JoshSilver8/MPPT-Charge-Controller/Photos/3D Model Rev 2.png

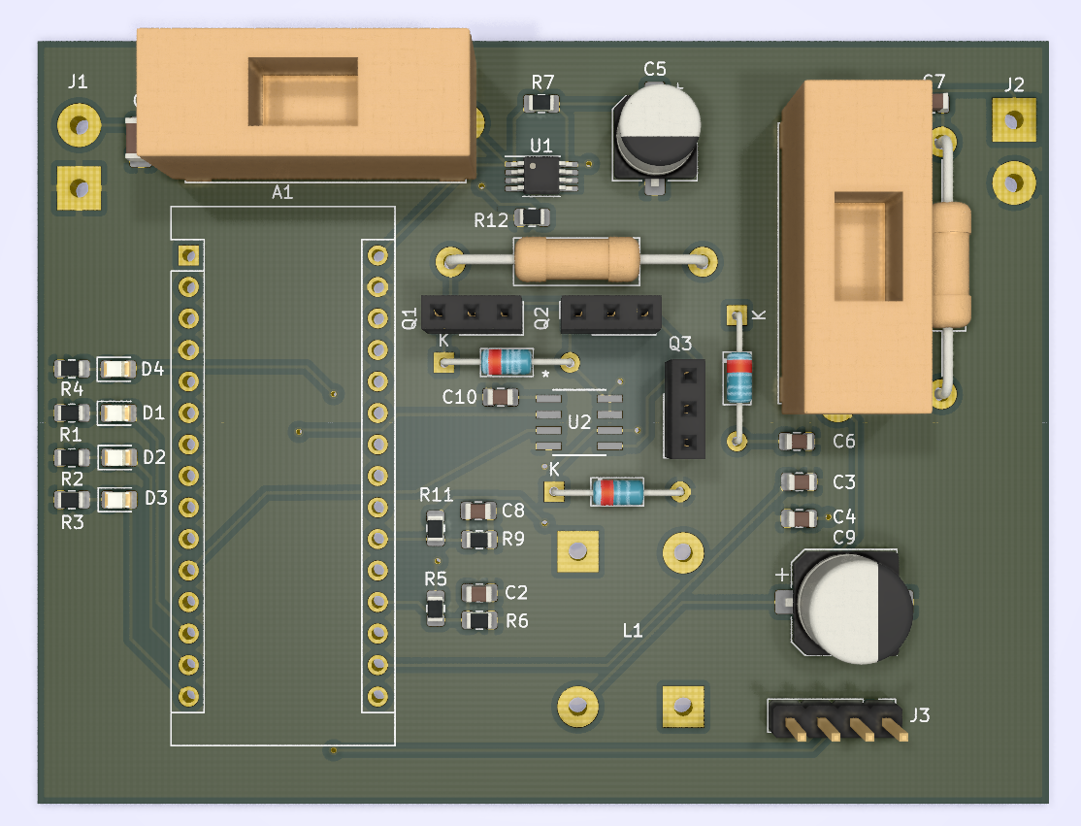
Photos/3D Model Rev 2.png
