JoshSilver8/MPPT-Charge-Controller/Photos/Buck Converter.png

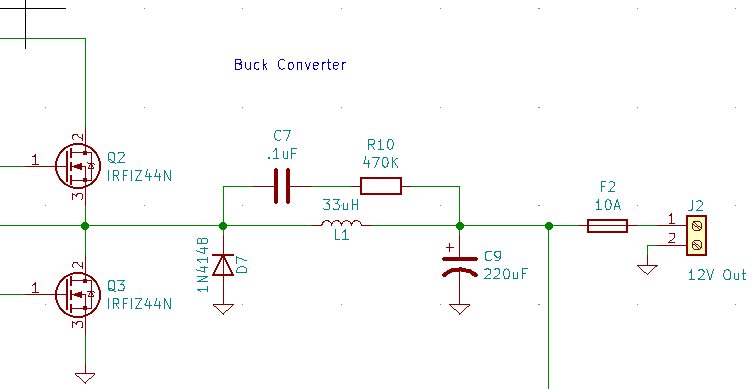
Photos/Buck Converter.png
