JoshSilver8/MPPT-Charge-Controller/Photos/Current and Voltage Sense.png

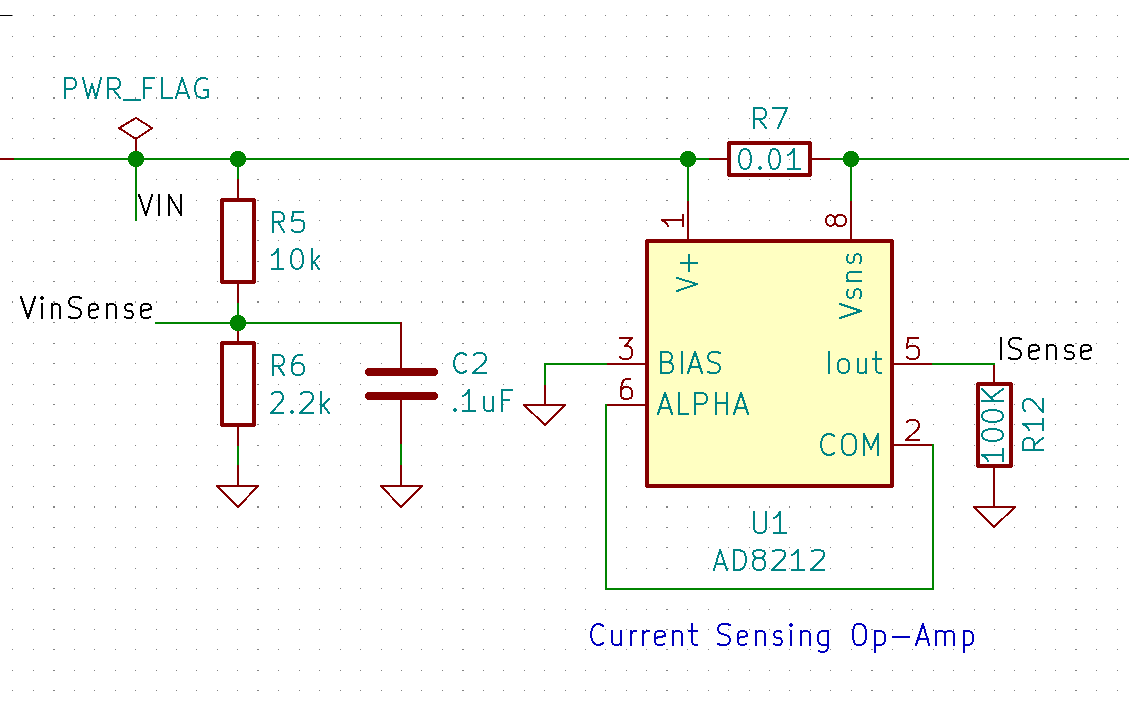
Photos/Current and Voltage Sense.png
