JoshSilver8/MPPT-Charge-Controller/Photos/Current Sense Config.png

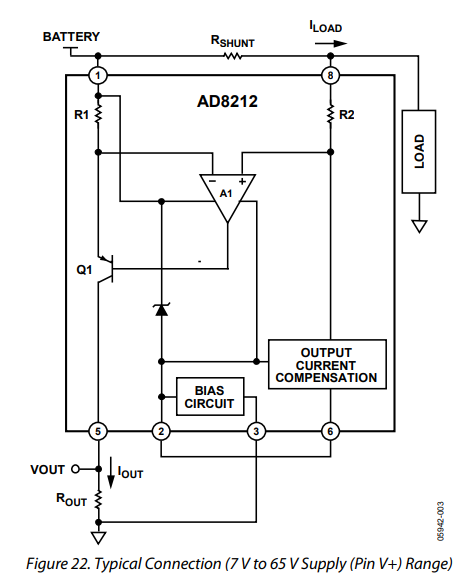
Photos/Current Sense Config.png
