JoshSilver8/MPPT-Charge-Controller/Photos/Discharge Prevention.png

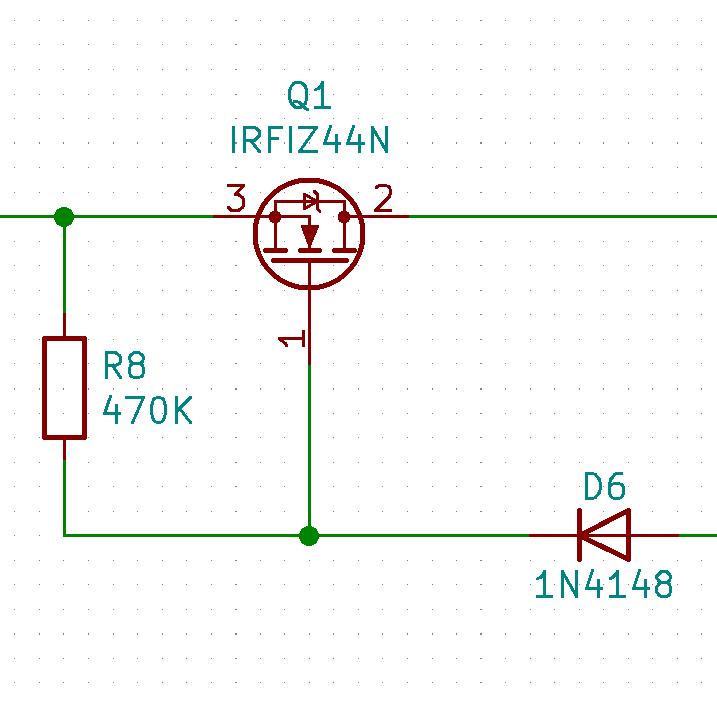
Photos/Discharge Prevention.png
