JoshSilver8/MPPT-Charge-Controller/Photos/MPPT Charge Controller Sch.png

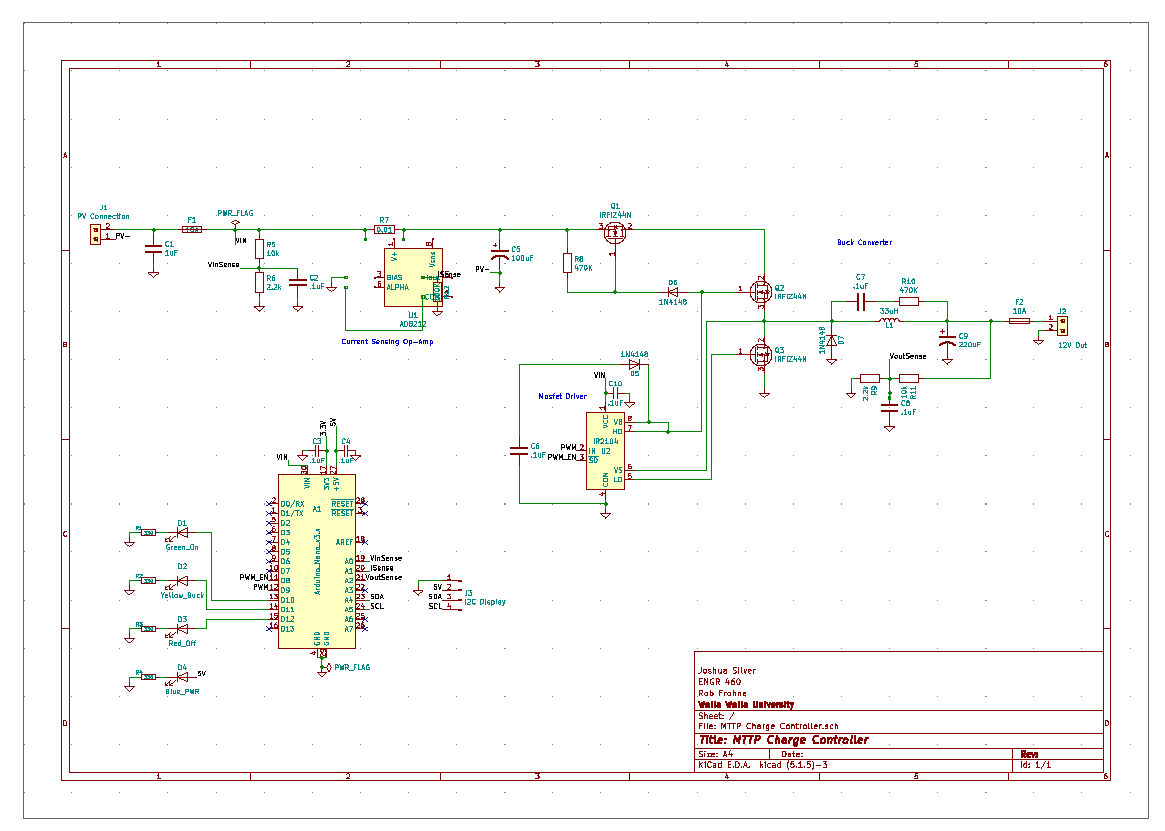
Photos/MPPT Charge Controller Sch.png
