JoshSilver8/MPPT-Charge-Controller/Photos/MPPT LED Output.png

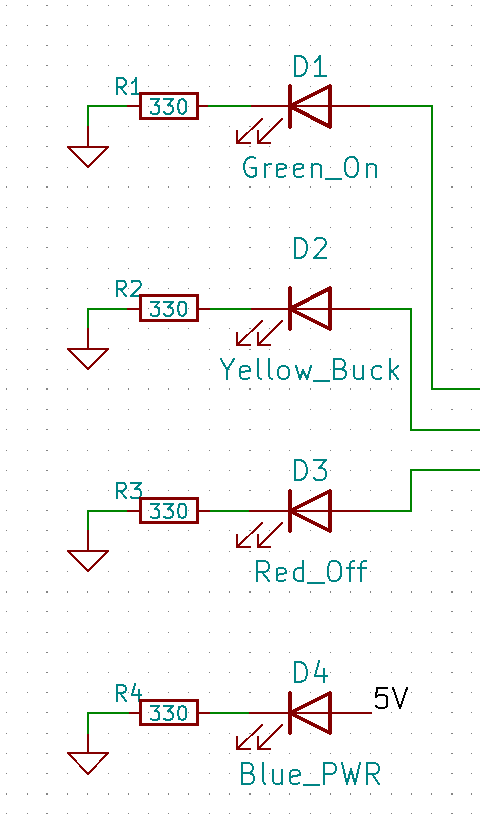
Photos/MPPT LED Output.png
