JoshSilver8/MPPT-Charge-Controller/Photos/Screen.png

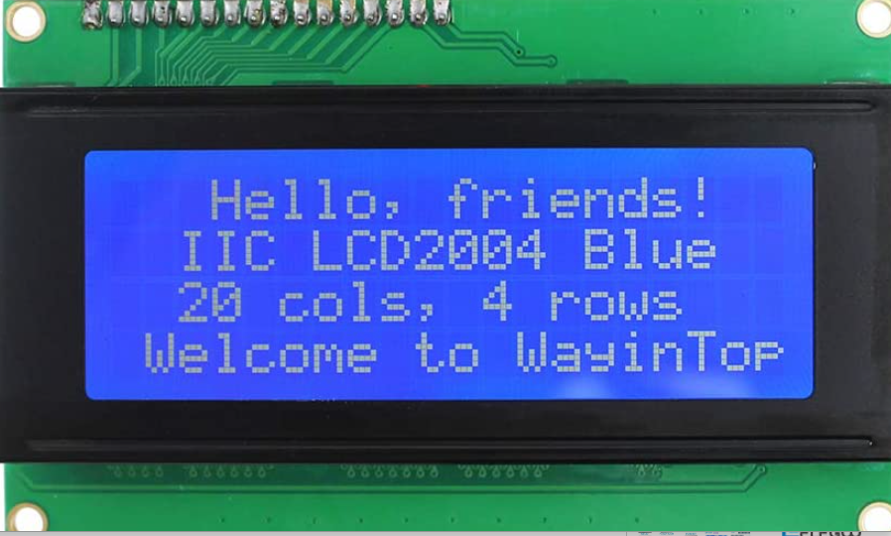
Photos/Screen.png
